ValentiWorkLearning/stm32f4_sdram_baseboard/cube_project/Core/Inc/sdram.h

/*
 * sdram_defs.h
 *
 *  Created on: 2 Dec 2022
 *      Author: Valenti
 */

#ifndef INC_SDRAM_H_
#define INC_SDRAM_H_

#include <stdint.h>
#include "stm32f4xx.h"
#include "stm32f4xx_hal_sdram.h"


#define   SDRAM_OK         ((uint8_t)0x00)
#define   SDRAM_ERROR      ((uint8_t)0x01)

/**
  * @brief  FMC SDRAM Bank address
  */
#define SDRAM_DEVICE_ADDR         ((uint32_t)0xD0000000)
#define SDRAM_DEVICE_SIZE         ((uint32_t)0x800000)  /* SDRAM device size in Bytes */

/**
  * @brief  FMC SDRAM Memory Width
  */
/* #define SDRAM_MEMORY_WIDTH   FMC_SDRAM_MEM_BUS_WIDTH_8 */
#define SDRAM_MEMORY_WIDTH      FMC_SDRAM_MEM_BUS_WIDTH_16

/**
  * @brief  FMC SDRAM CAS Latency
  */
/* #define SDRAM_CAS_LATENCY    FMC_SDRAM_CAS_LATENCY_2 */
#define SDRAM_CAS_LATENCY       FMC_SDRAM_CAS_LATENCY_3

/**
  * @brief  FMC SDRAM Memory clock period
  */
#define SDCLOCK_PERIOD          FMC_SDRAM_CLOCK_PERIOD_2    /* Default configuration used with LCD */
/* #define SDCLOCK_PERIOD       FMC_SDRAM_CLOCK_PERIOD_3 */

/**
  * @brief  FMC SDRAM Memory Read Burst feature
  */
#define SDRAM_READBURST         FMC_SDRAM_RBURST_DISABLE    /* Default configuration used with LCD */
/* #define SDRAM_READBURST      FMC_SDRAM_RBURST_ENABLE */

/**
  * @brief  FMC SDRAM Bank Remap
  */
/* #define SDRAM_BANK_REMAP */


#define SDRAM_MODEREG_BURST_LENGTH_1             ((uint16_t)0x0000)
#define SDRAM_MODEREG_BURST_LENGTH_2             ((uint16_t)0x0001)
#define SDRAM_MODEREG_BURST_LENGTH_4             ((uint16_t)0x0002)
#define SDRAM_MODEREG_BURST_LENGTH_8             ((uint16_t)0x0004)
#define SDRAM_MODEREG_BURST_TYPE_SEQUENTIAL      ((uint16_t)0x0000)
#define SDRAM_MODEREG_BURST_TYPE_INTERLEAVED     ((uint16_t)0x0008)
#define SDRAM_MODEREG_CAS_LATENCY_2              ((uint16_t)0x0020)
#define SDRAM_MODEREG_CAS_LATENCY_3              ((uint16_t)0x0030)
#define SDRAM_MODEREG_OPERATING_MODE_STANDARD    ((uint16_t)0x0000)
#define SDRAM_MODEREG_WRITEBURST_MODE_PROGRAMMED ((uint16_t)0x0000)
#define SDRAM_MODEREG_WRITEBURST_MODE_SINGLE     ((uint16_t)0x0200)


void bsp_sdram_init(SDRAM_HandleTypeDef* pSdramHandle);
uint8_t bsp_sdram_perform_test(SDRAM_HandleTypeDef* pSdramHandle);

#endif /* INC_SDRAM_H_ */
